AntonioGarosi/Heap/Electronic boards/core-controller/drawings/002-drills.png

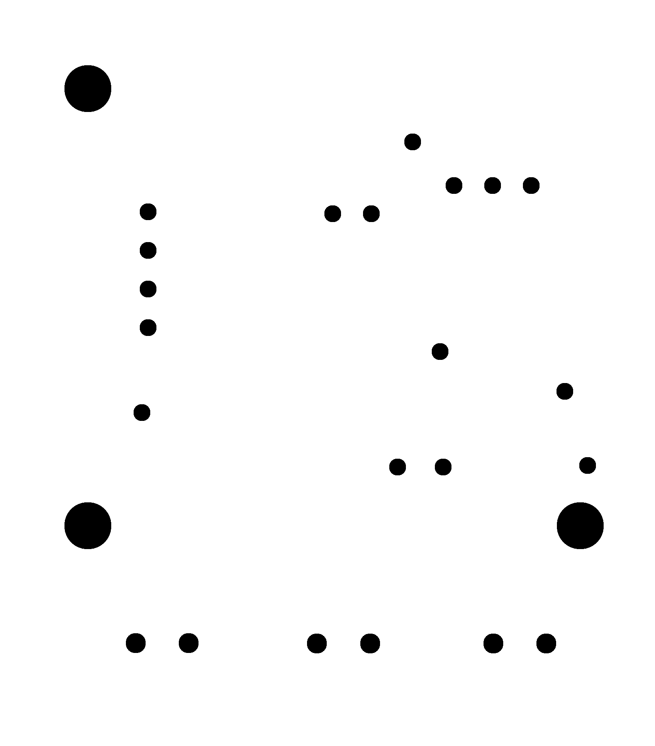
Electronic boards/core-controller/drawings/002-drills.png
