AntonioGarosi/Heap/Electronic boards/core-controller/drawings/003-outline.png

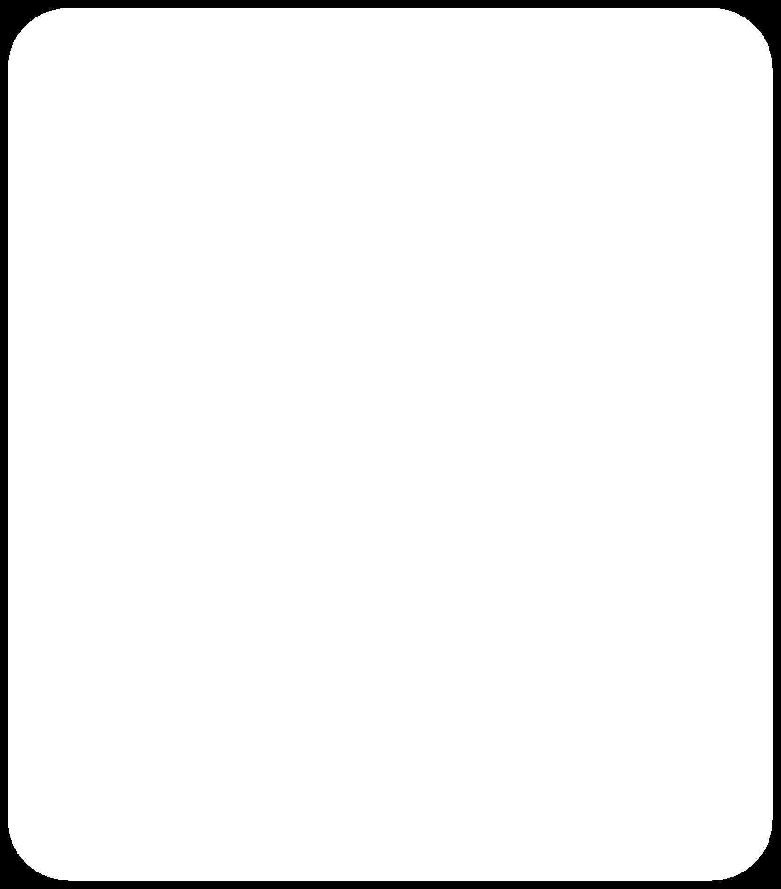
Electronic boards/core-controller/drawings/003-outline.png
