AntonioGarosi/Heap/Electronic boards/core-controller/drawings/layout.png

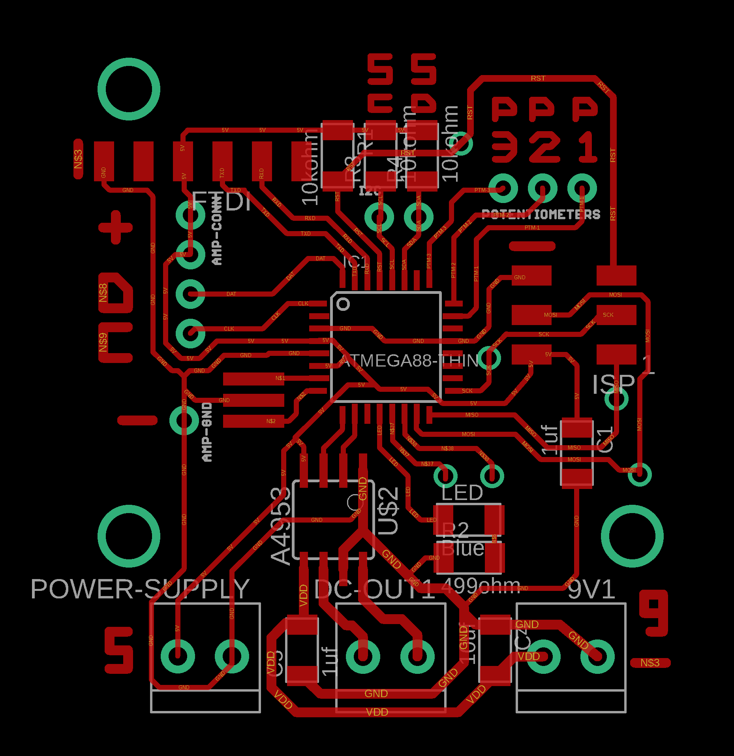
Electronic boards/core-controller/drawings/layout.png
