AntonioGarosi/Heap/Electronic boards/power-supply/drawings/001-traces.png

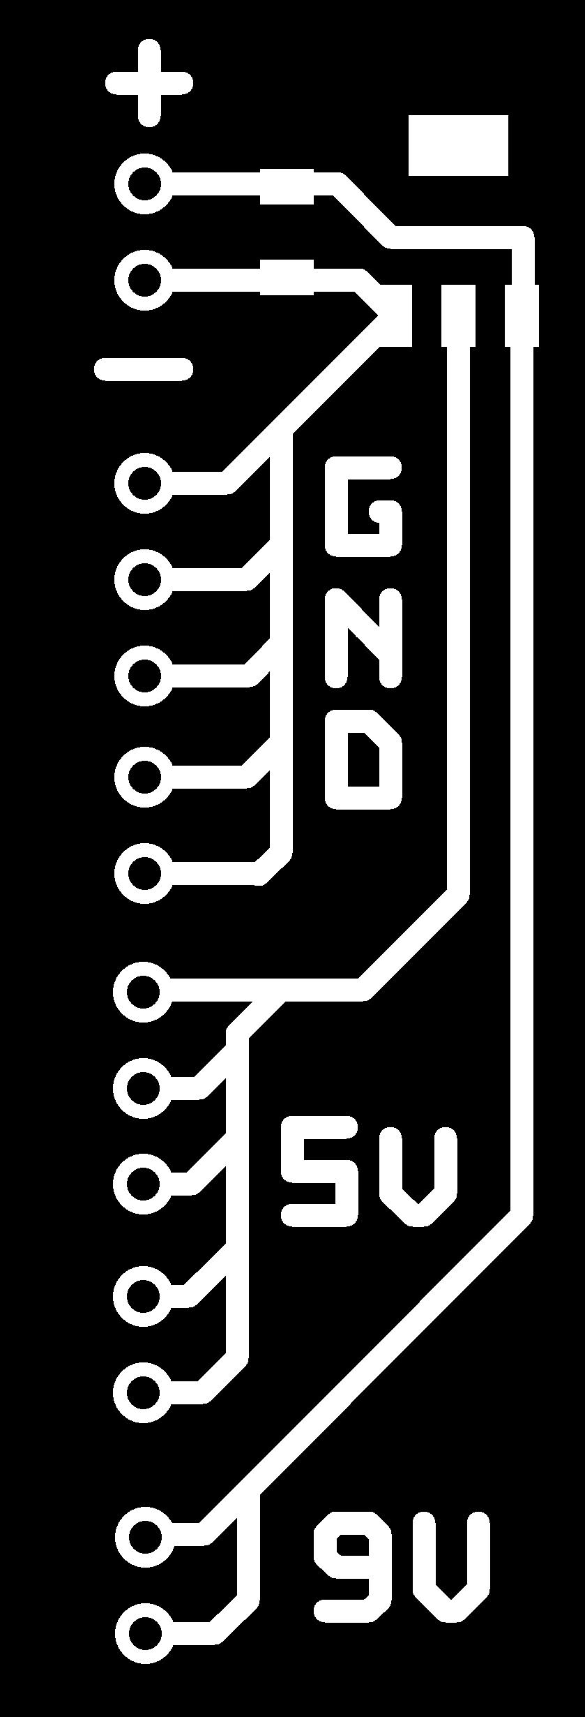
Electronic boards/power-supply/drawings/001-traces.png
