AntonioGarosi/Heap/Electronic boards/power-supply/drawings/002-drills.png

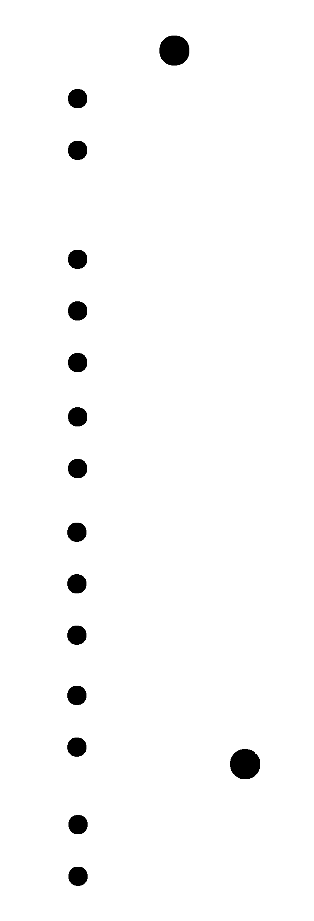
Electronic boards/power-supply/drawings/002-drills.png
