AntonioGarosi/Heap/Electronic boards/power-supply/drawings/layout.png

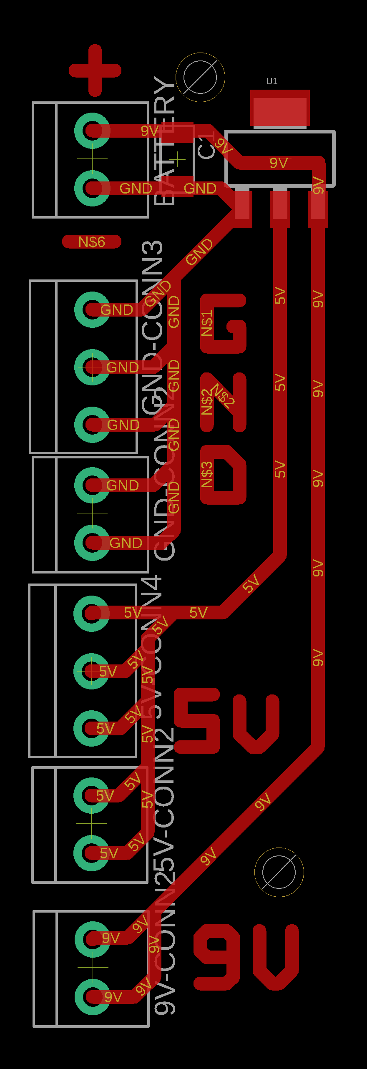
Electronic boards/power-supply/drawings/layout.png
