AntonioGarosi/Heap/Electronic boards/speaker-driver/drawings/001- traces.png

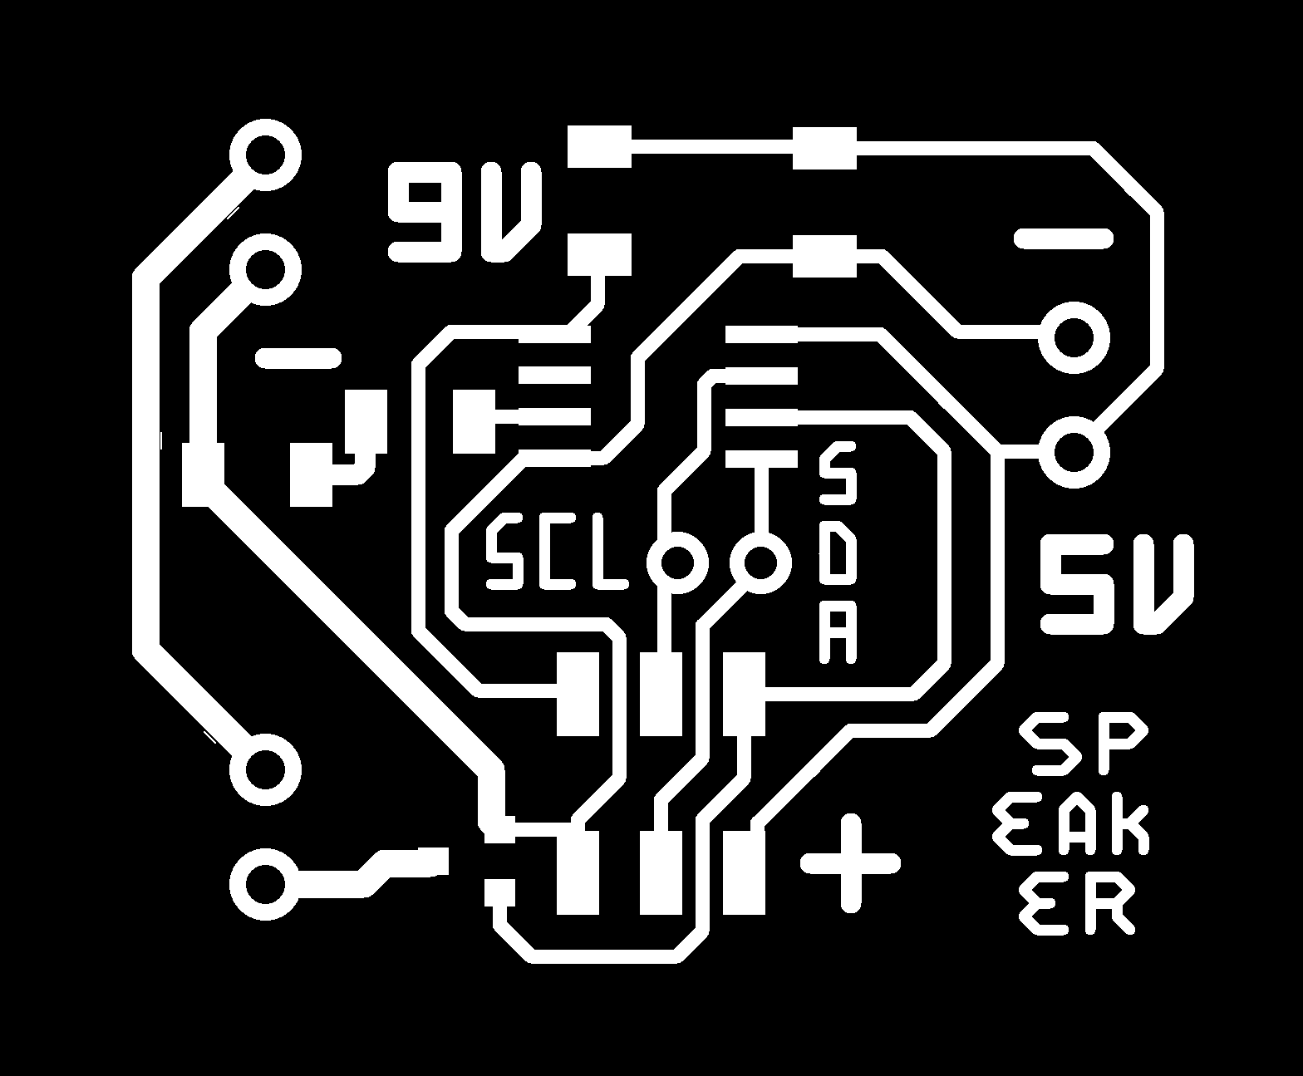
Electronic boards/speaker-driver/drawings/001- traces.png
