AntonioGarosi/Heap/Electronic boards/speaker-driver/drawings/002 - drills.png

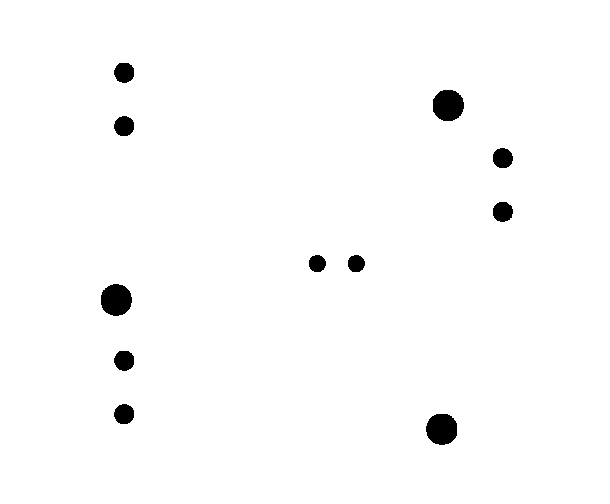
Electronic boards/speaker-driver/drawings/002 - drills.png
