AntonioGarosi/Heap/Electronic boards/speaker-driver/drawings/schematic.png

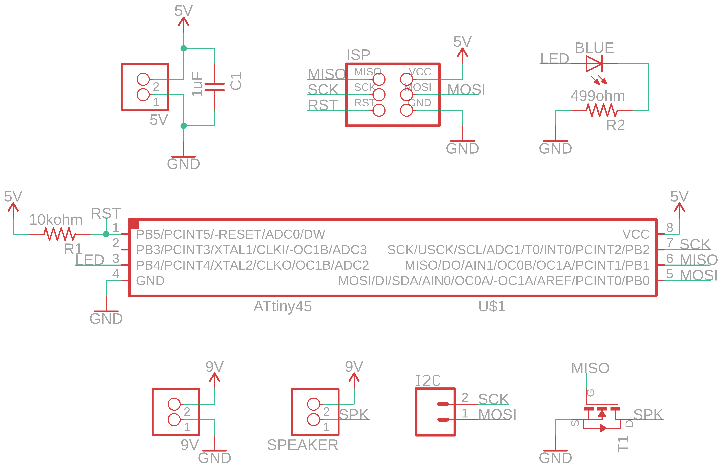
Electronic boards/speaker-driver/drawings/schematic.png
