AntonioGarosi/Heap/First prototype/Electronic boards/core-controller/drawings/001-traces.png

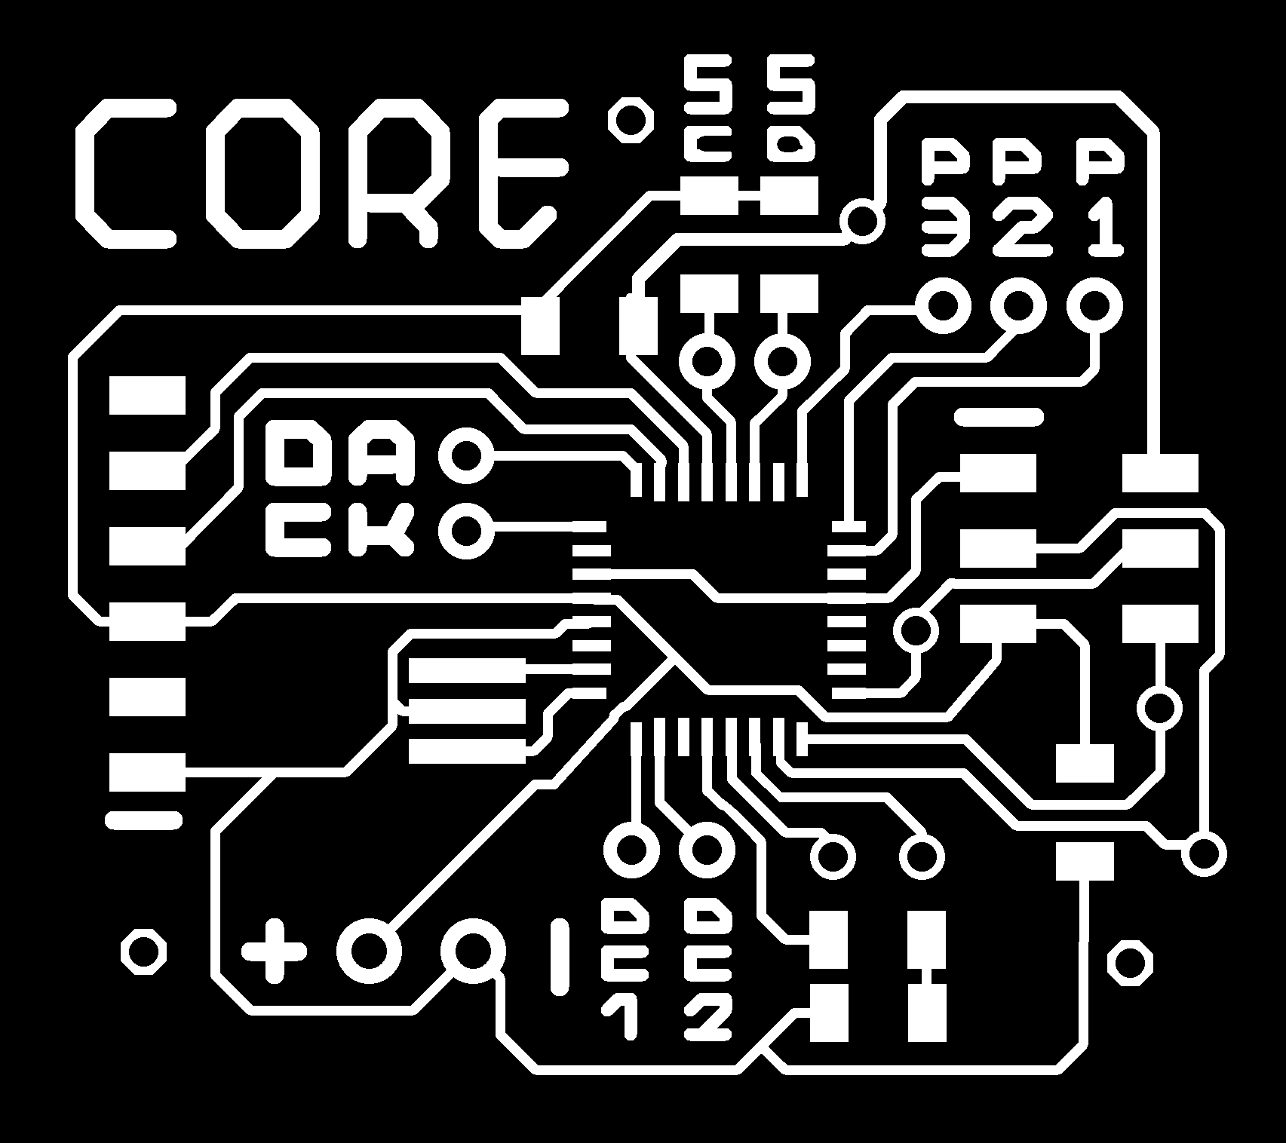
First prototype/Electronic boards/core-controller/drawings/001-traces.png
