AntonioGarosi/Heap/First prototype/Electronic boards/core-controller/drawings/002-drills.png

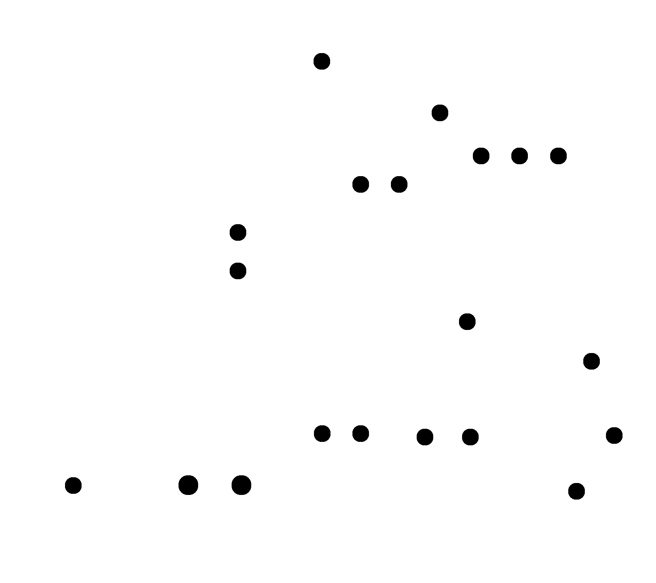
First prototype/Electronic boards/core-controller/drawings/002-drills.png
