AntonioGarosi/Heap/First prototype/Electronic boards/dc-driver/drawings/001-traces.png

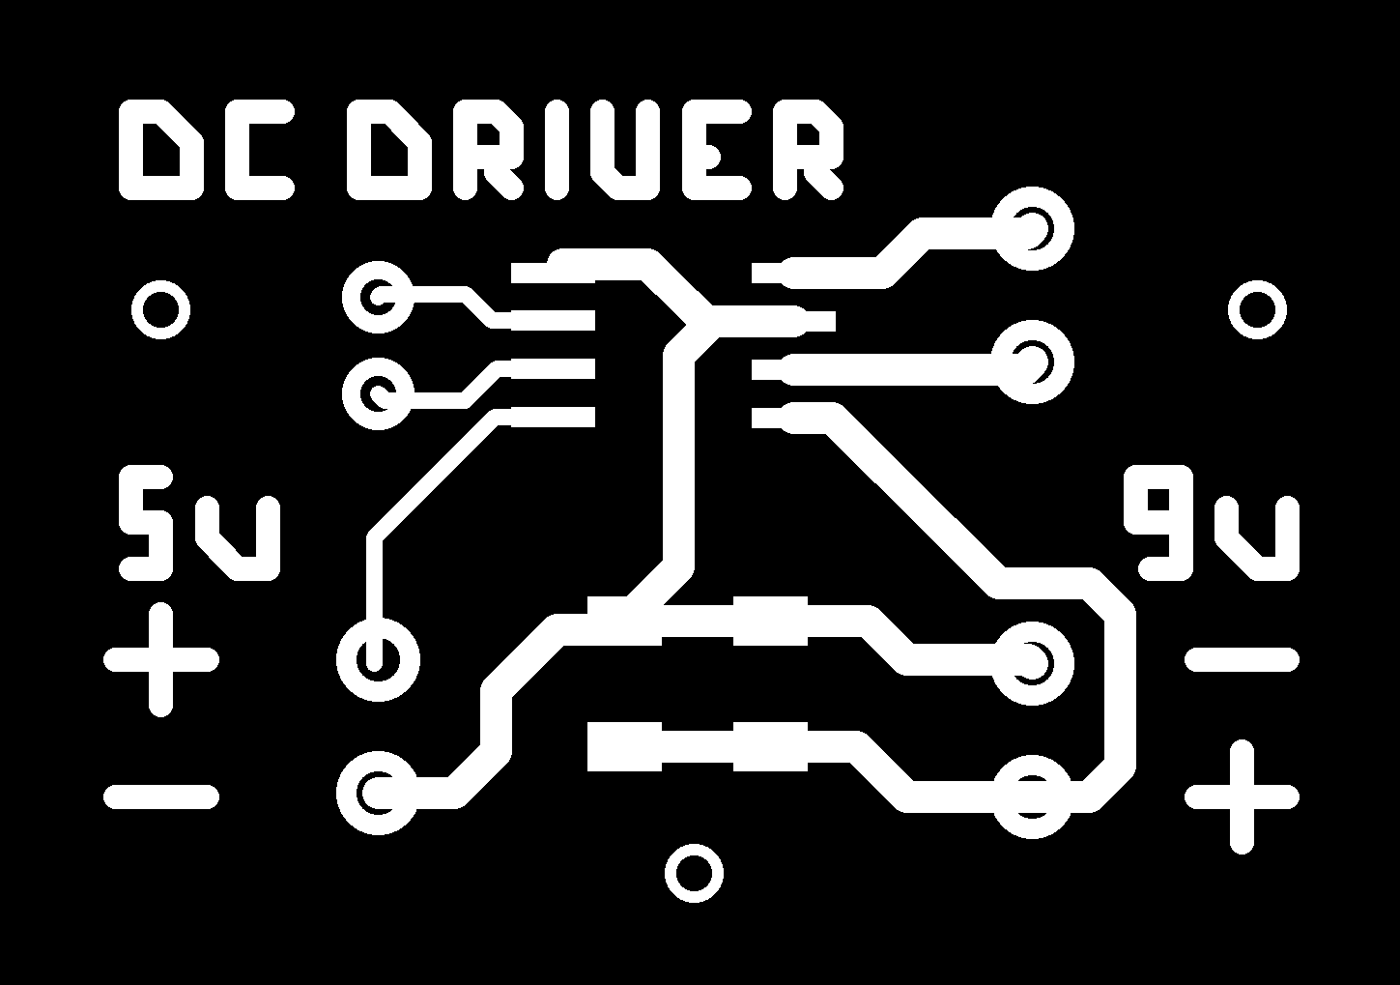
First prototype/Electronic boards/dc-driver/drawings/001-traces.png
