AntonioGarosi/Heap/First prototype/Electronic boards/dc-driver/drawings/002-drills.png

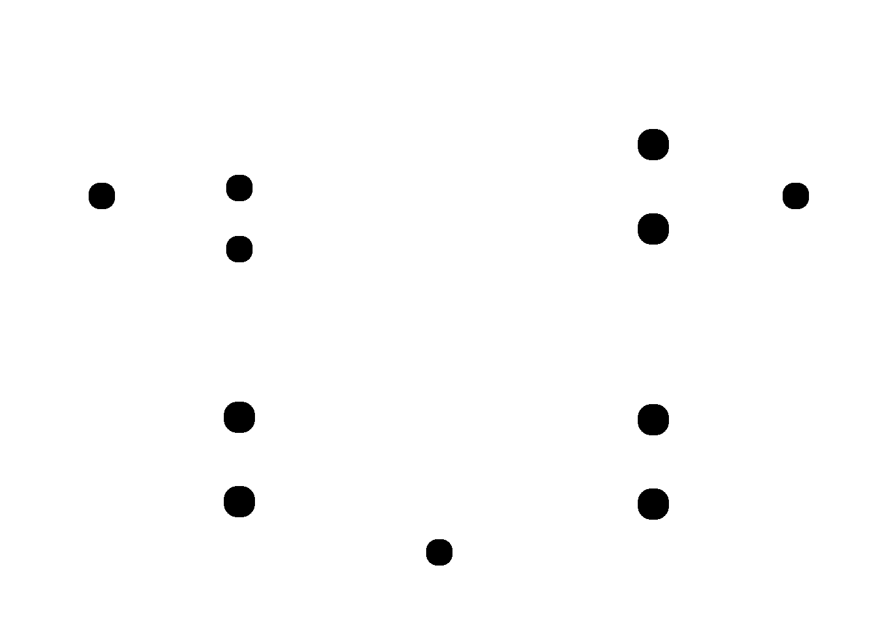
First prototype/Electronic boards/dc-driver/drawings/002-drills.png
