AntonioGarosi/Heap/First prototype/Electronic boards/power-supply/drawings/001-traces.png

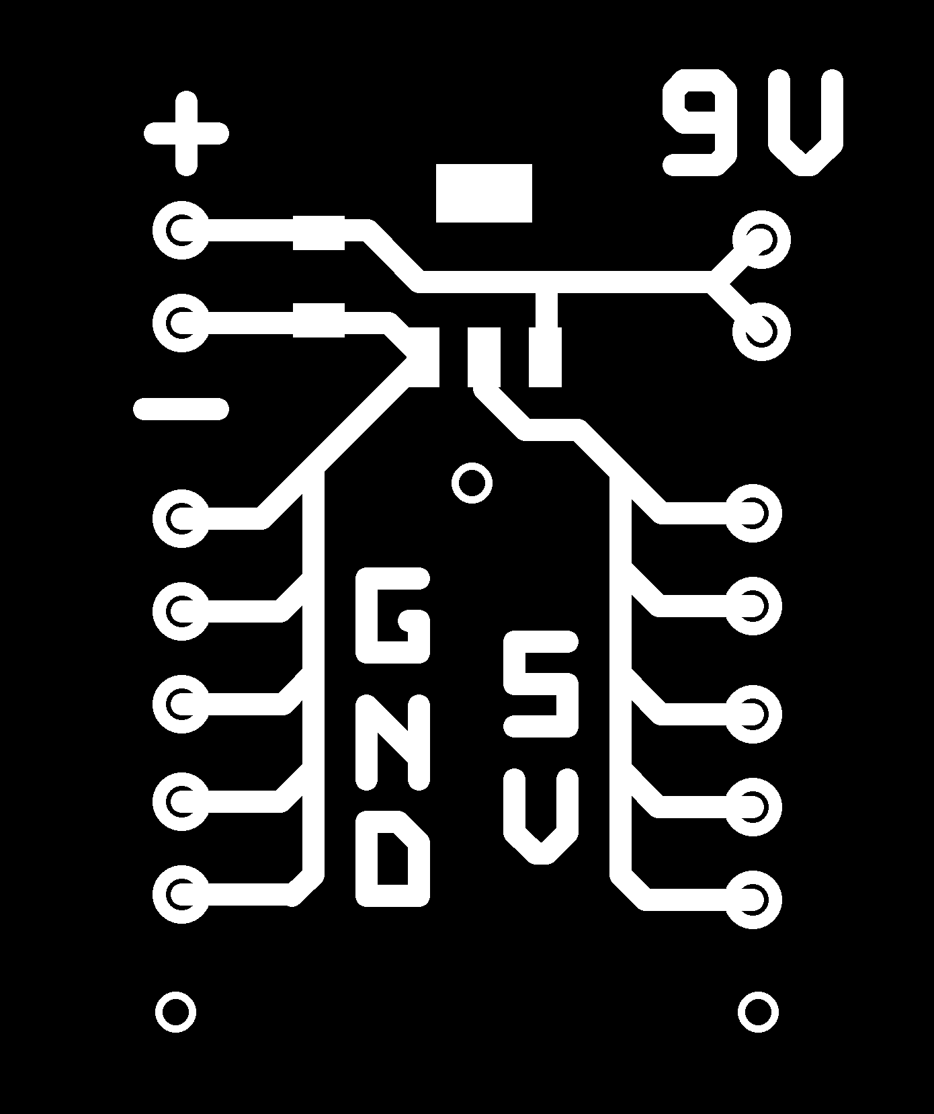
First prototype/Electronic boards/power-supply/drawings/001-traces.png
