AntonioGarosi/Heap/First prototype/Electronic boards/power-supply/drawings/002-holes.png

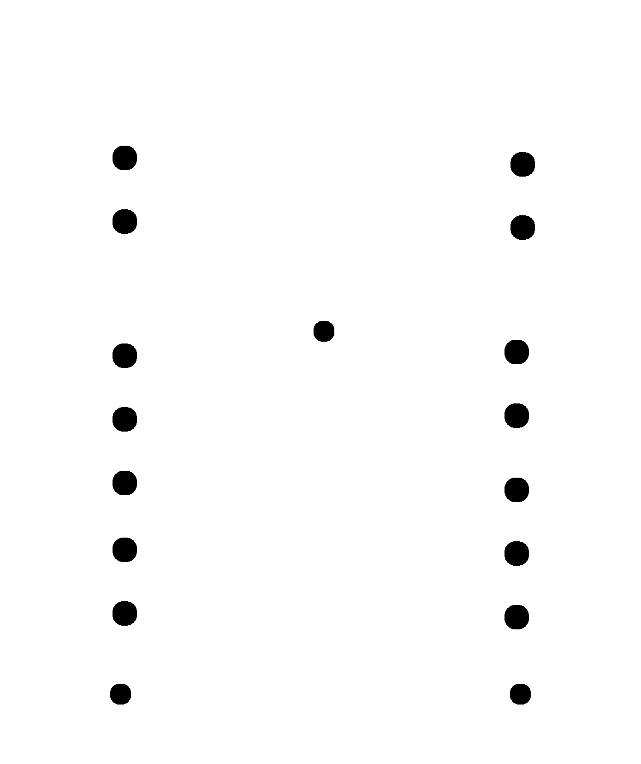
First prototype/Electronic boards/power-supply/drawings/002-holes.png
