AntonioGarosi/Heap/First prototype/Graphic designs/Cards/Drawings/card-ball.png

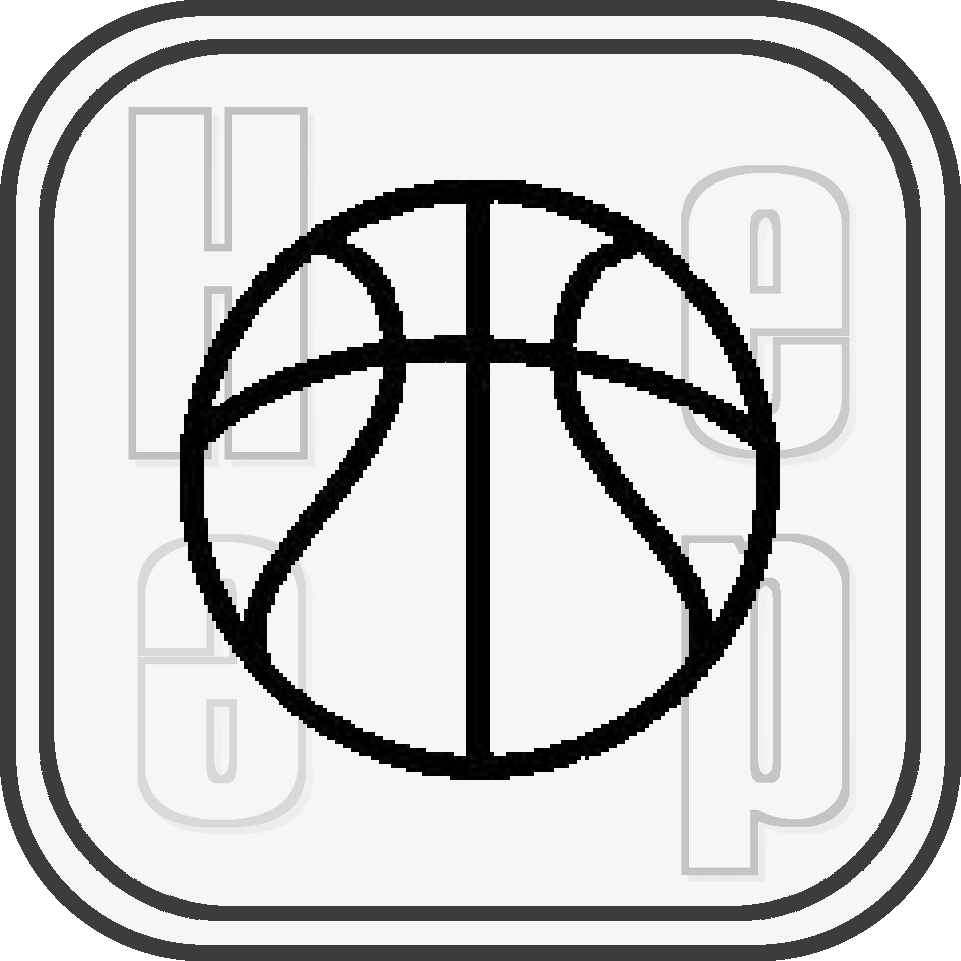
First prototype/Graphic designs/Cards/Drawings/card-ball.png
