AntonioGarosi/Heap/First prototype/Graphic designs/Cards/Drawings/card-book.png

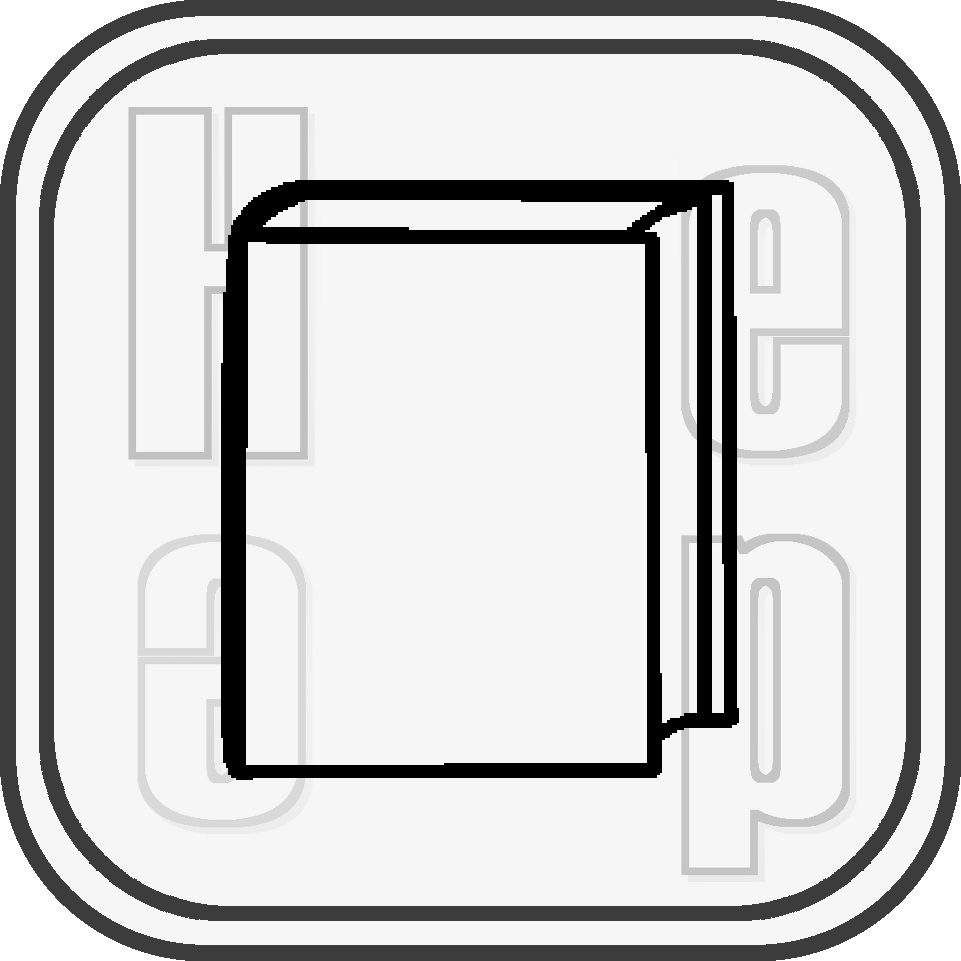
First prototype/Graphic designs/Cards/Drawings/card-book.png
