AntonioGarosi/Heap/First prototype/Graphic designs/Cards/Drawings/card-bottle.png

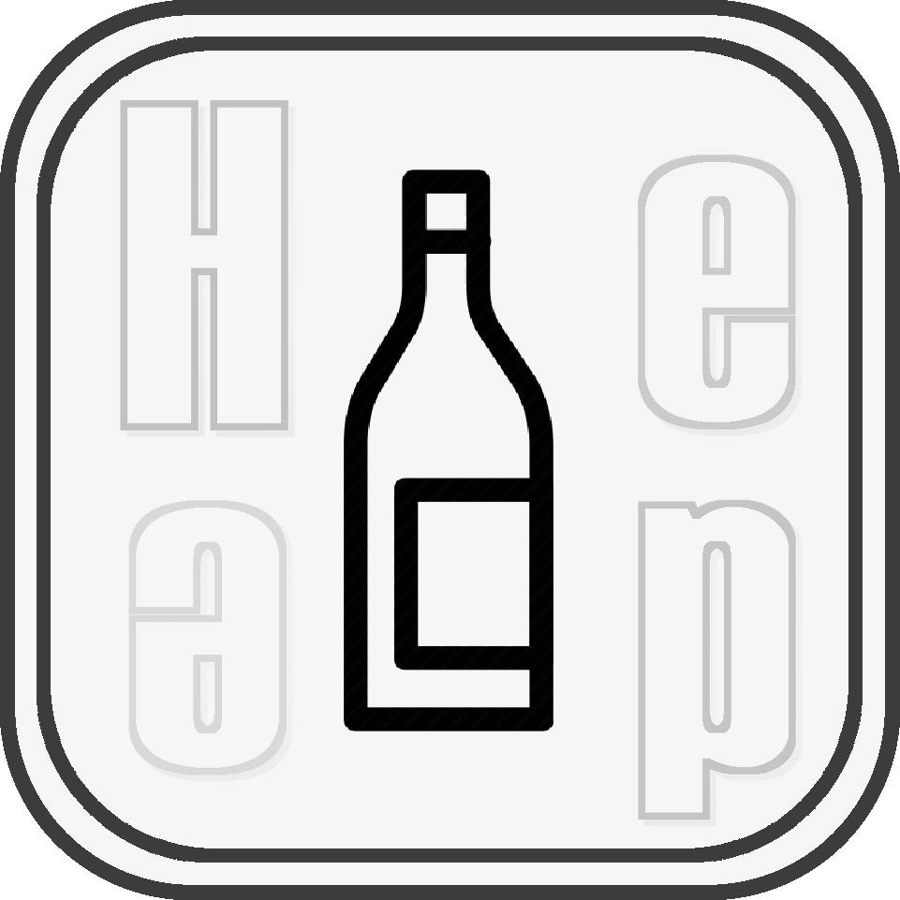
First prototype/Graphic designs/Cards/Drawings/card-bottle.png
