AntonioGarosi/Heap/First prototype/Graphic designs/Cards/Drawings/card-bottom.png

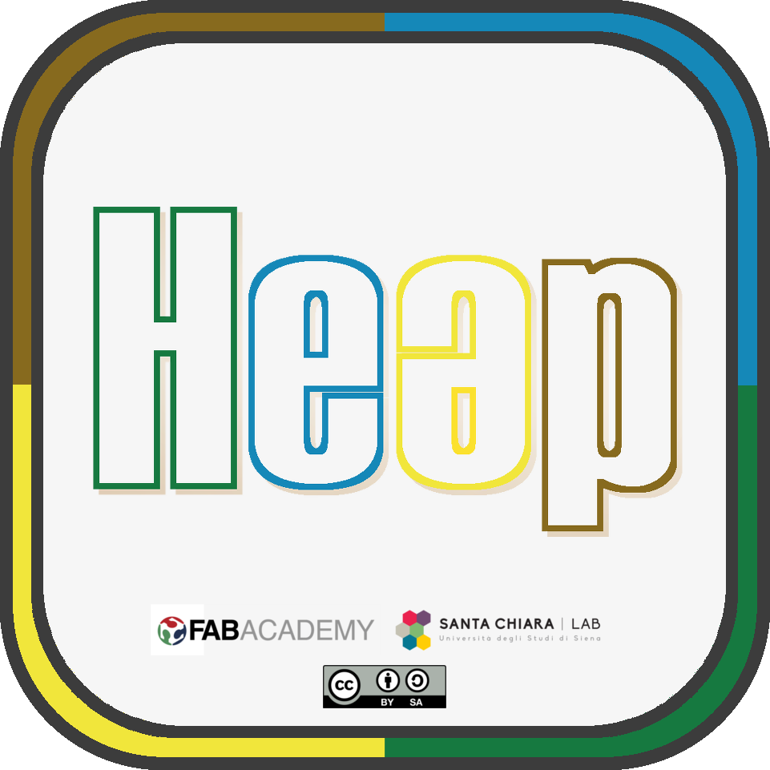
First prototype/Graphic designs/Cards/Drawings/card-bottom.png
