AntonioGarosi/Heap/First prototype/Graphic designs/Cards/Drawings/card-box.png

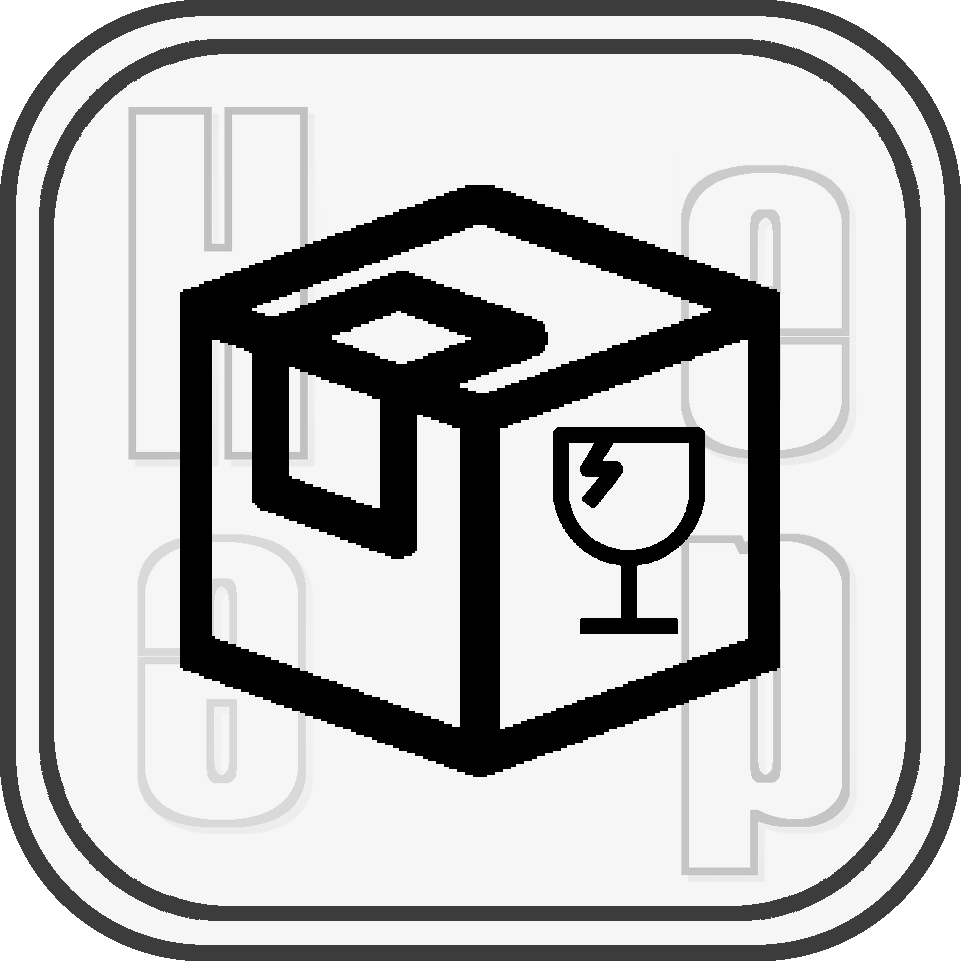
First prototype/Graphic designs/Cards/Drawings/card-box.png
