AntonioGarosi/Heap/First prototype/Graphic designs/Cards/Drawings/card-painting.png

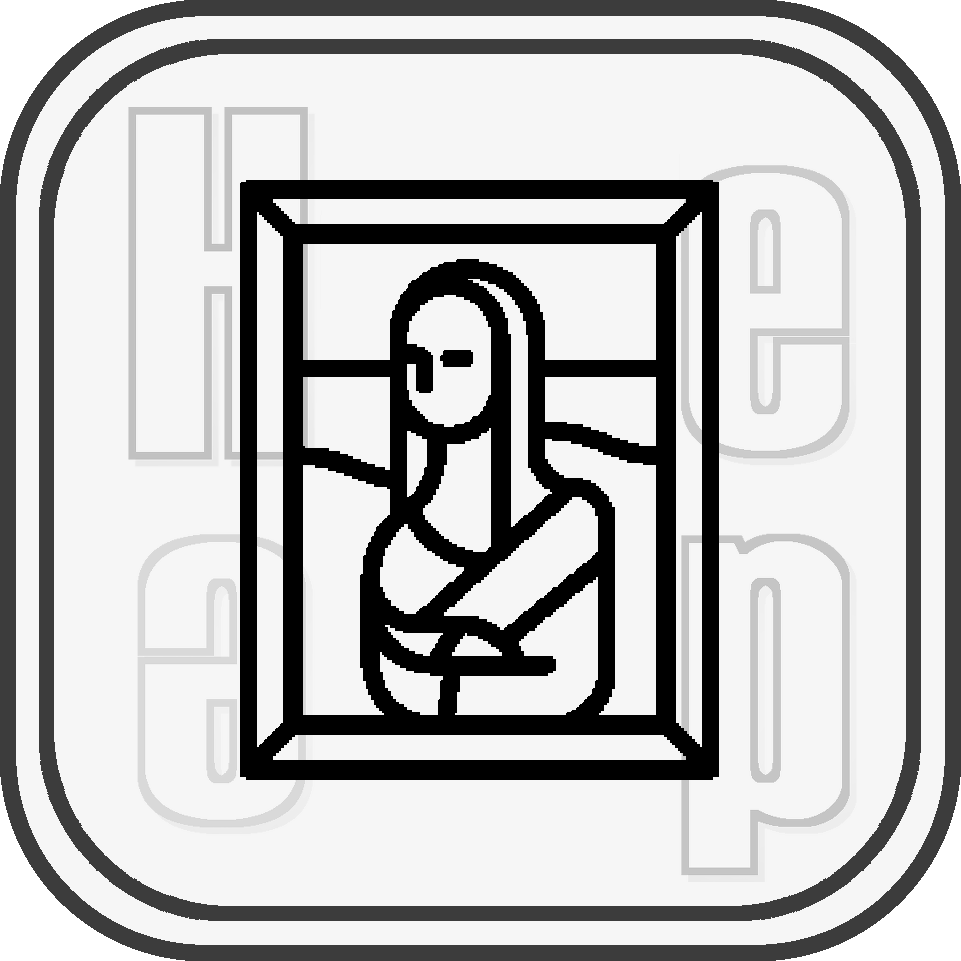
First prototype/Graphic designs/Cards/Drawings/card-painting.png
