AntonioGarosi/Heap/First prototype/Graphic designs/Cards/Drawings/card-paper-tissue.png

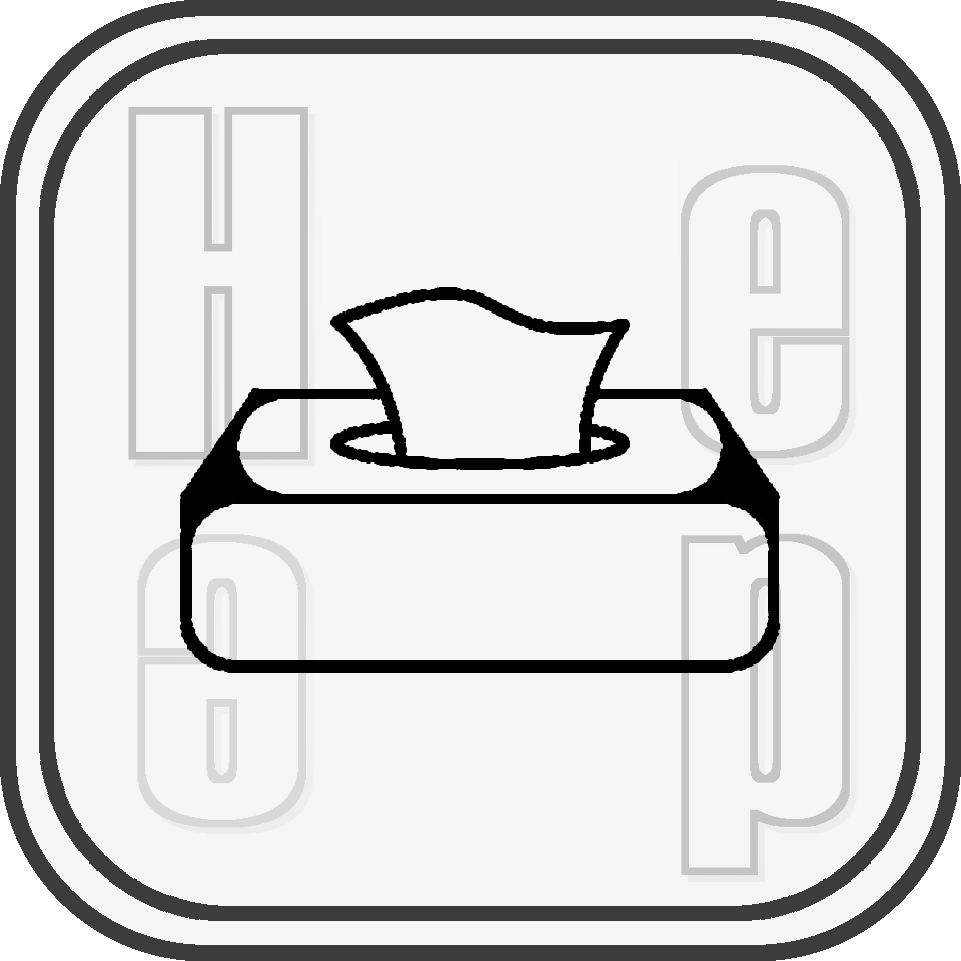
First prototype/Graphic designs/Cards/Drawings/card-paper-tissue.png
