AntonioGarosi/Heap/First prototype/Graphic designs/Cards/Drawings/card-top-template.png

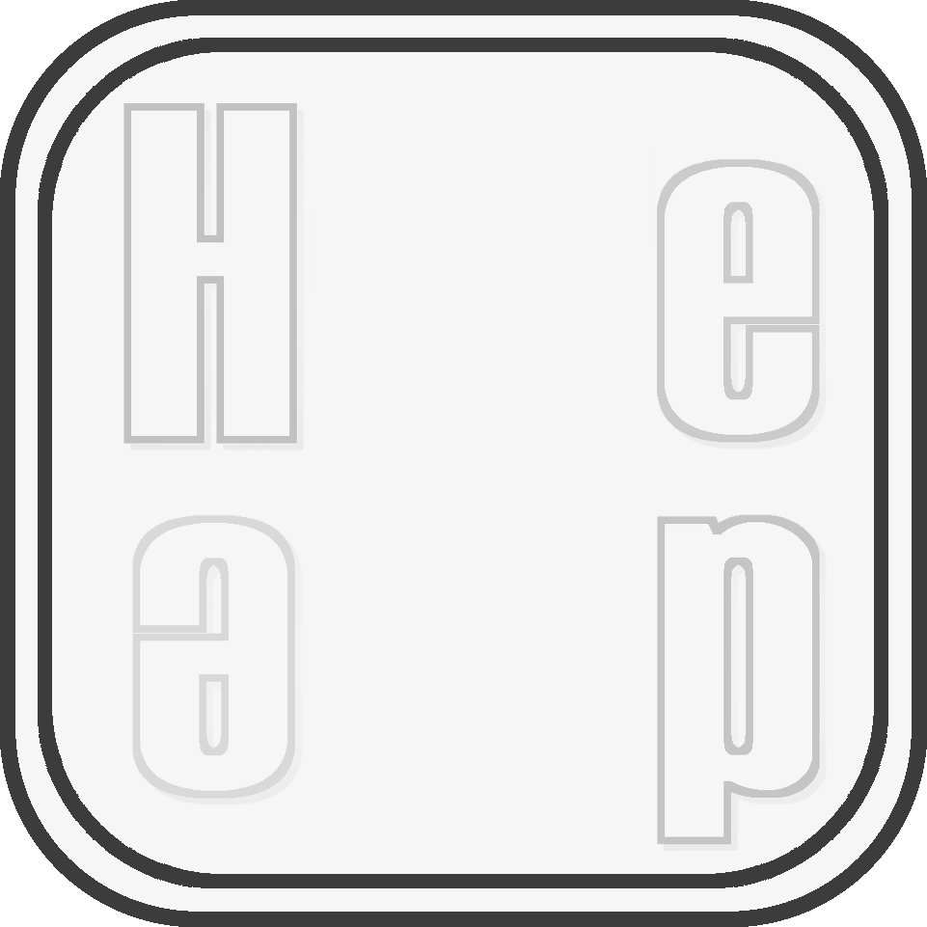
First prototype/Graphic designs/Cards/Drawings/card-top-template.png
