AntonioGarosi/Heap/First prototype/Graphic designs/Cards/Drawings/card-tv.png

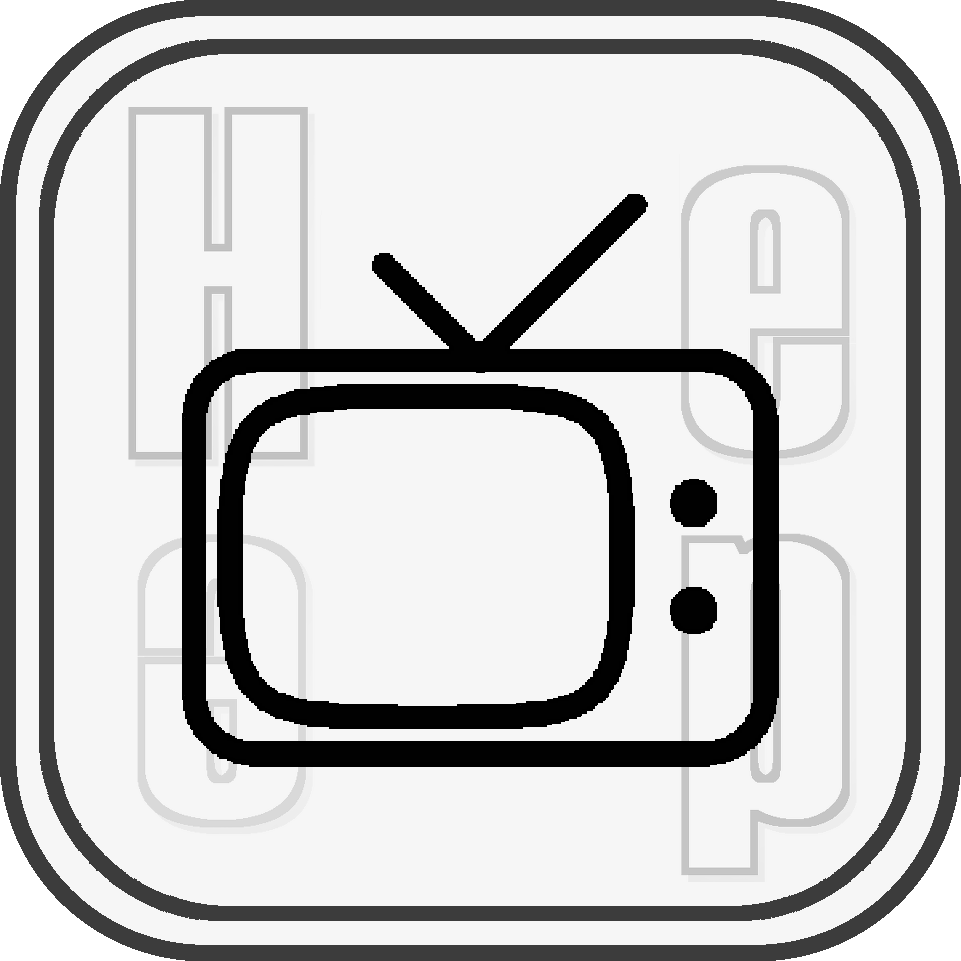
First prototype/Graphic designs/Cards/Drawings/card-tv.png
