AntonioGarosi/Heap/First prototype/Graphic designs/Cards/Drawings/card-umbrella.png

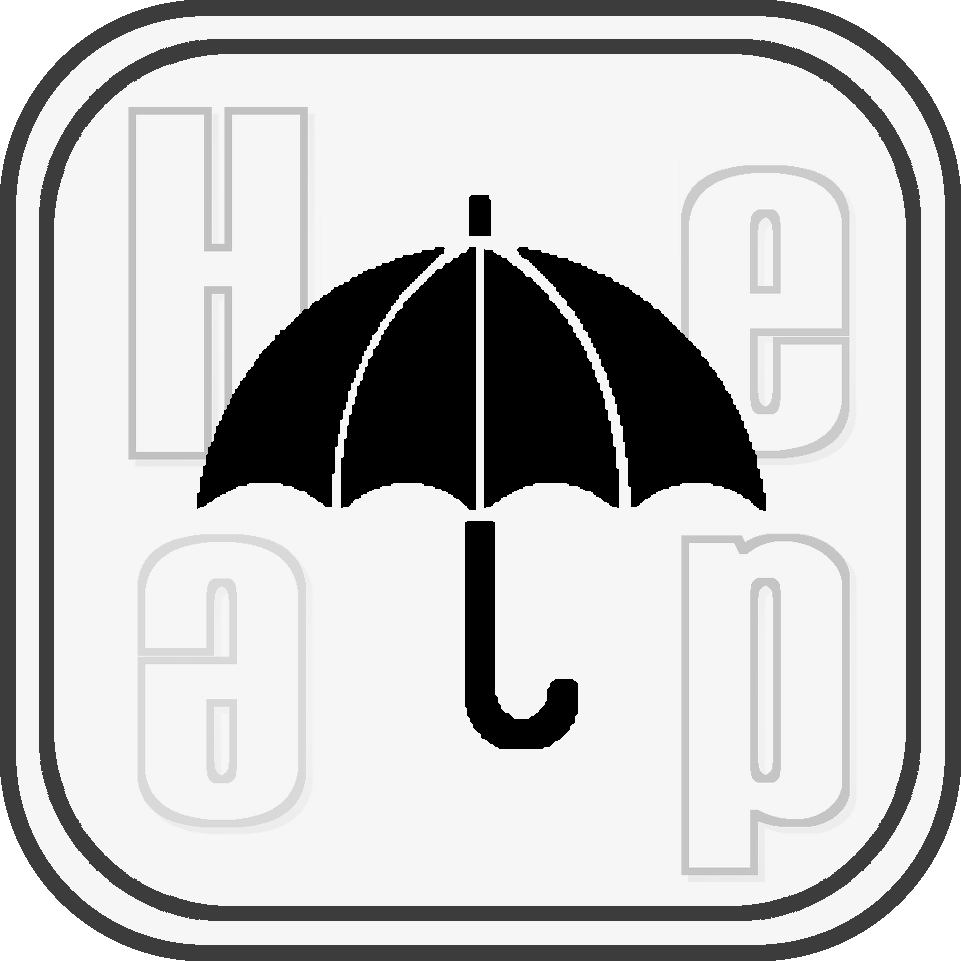
First prototype/Graphic designs/Cards/Drawings/card-umbrella.png
