AntonioGarosi/Heap/Graphic designs/Cards/Drawings/0.png

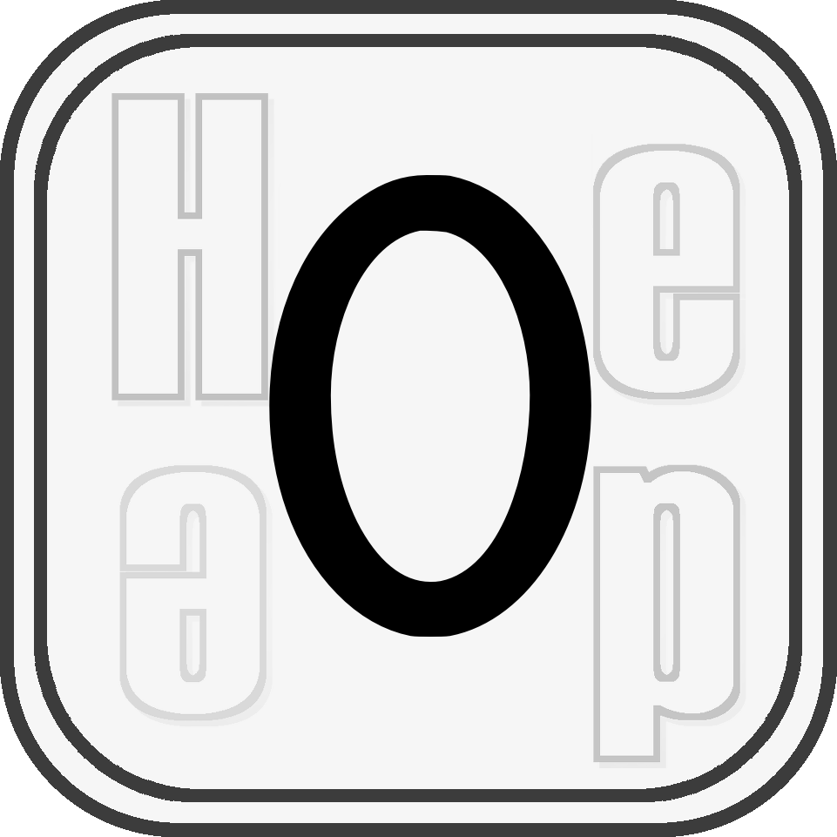
Graphic designs/Cards/Drawings/0.png
