AntonioGarosi/Heap/Graphic designs/Cards/Drawings/1.png

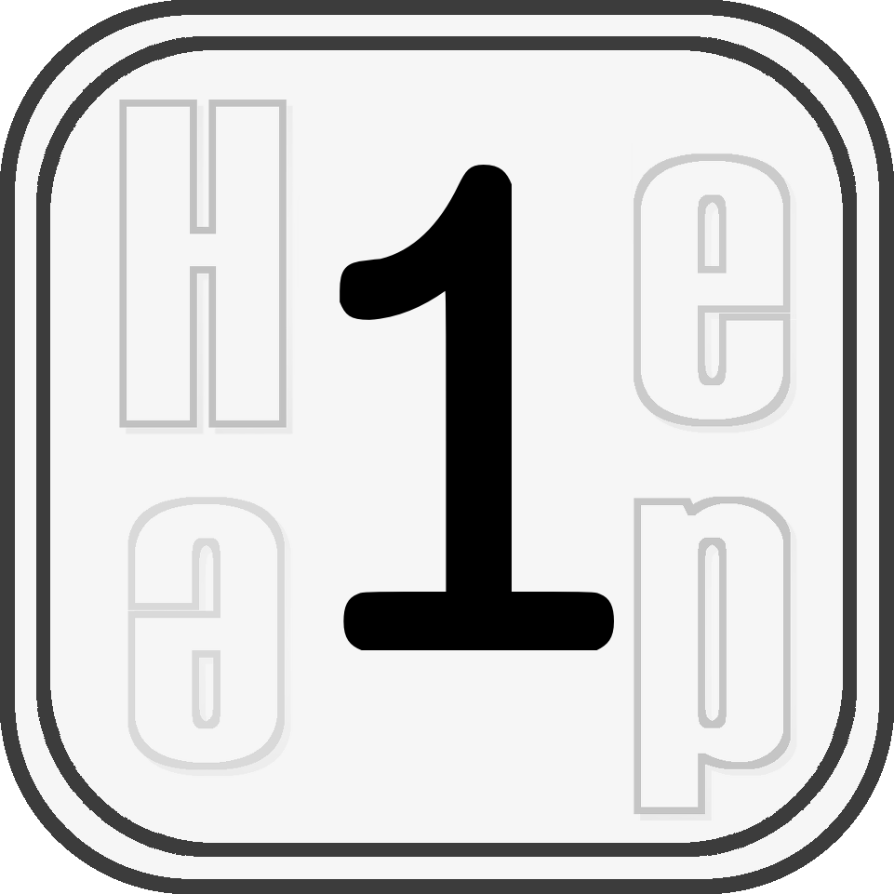
Graphic designs/Cards/Drawings/1.png
