AntonioGarosi/Heap/Graphic designs/Cards/Drawings/2.png

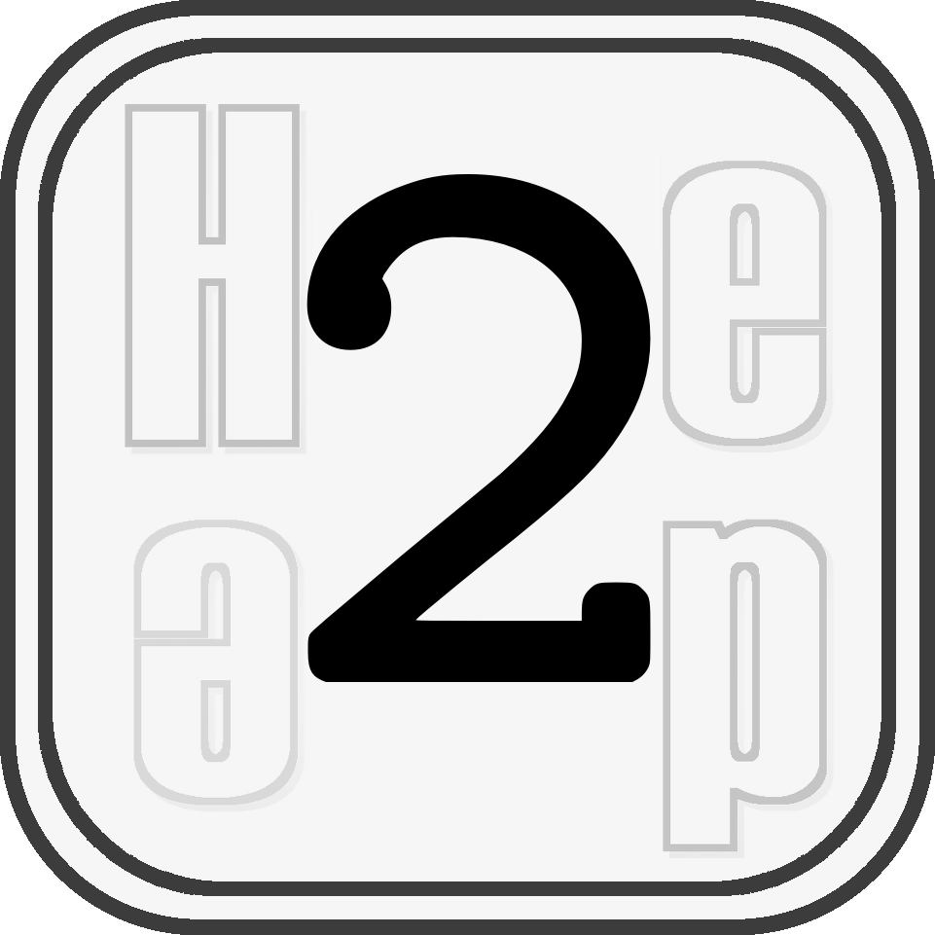
Graphic designs/Cards/Drawings/2.png
