AntonioGarosi/Heap/Graphic designs/Cards/Drawings/3.png

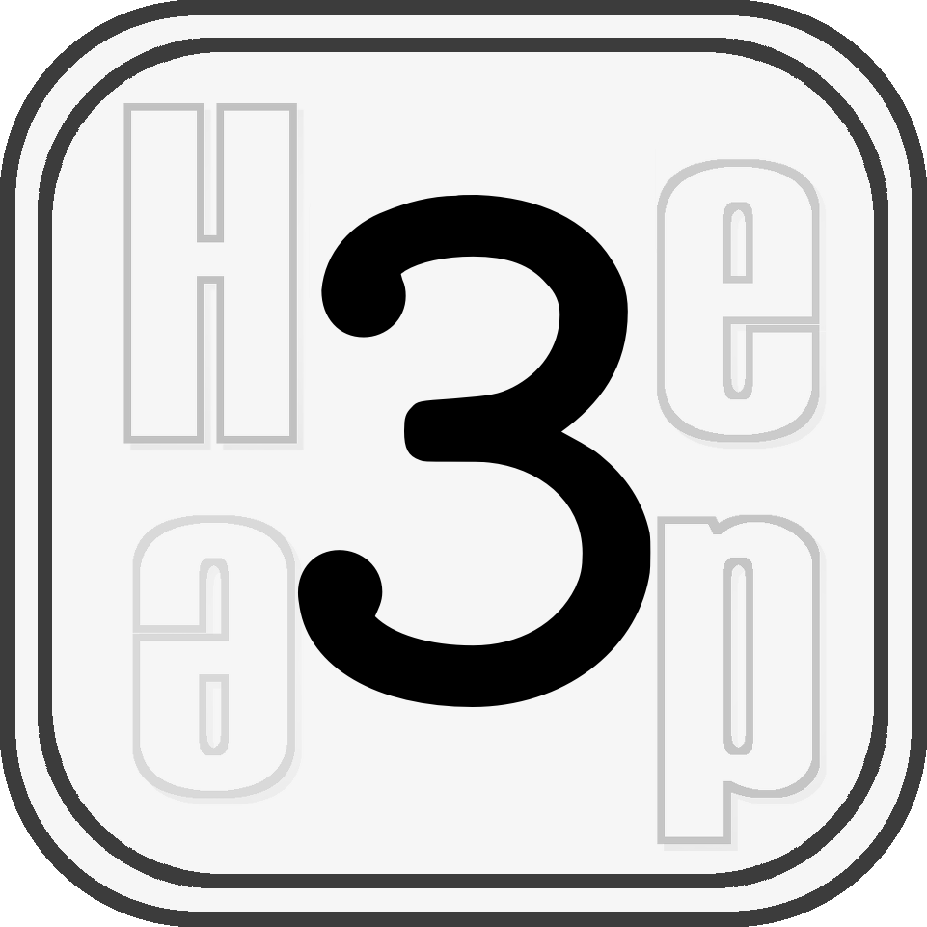
Graphic designs/Cards/Drawings/3.png
