AntonioGarosi/Heap/Graphic designs/Cards/Drawings/4.png

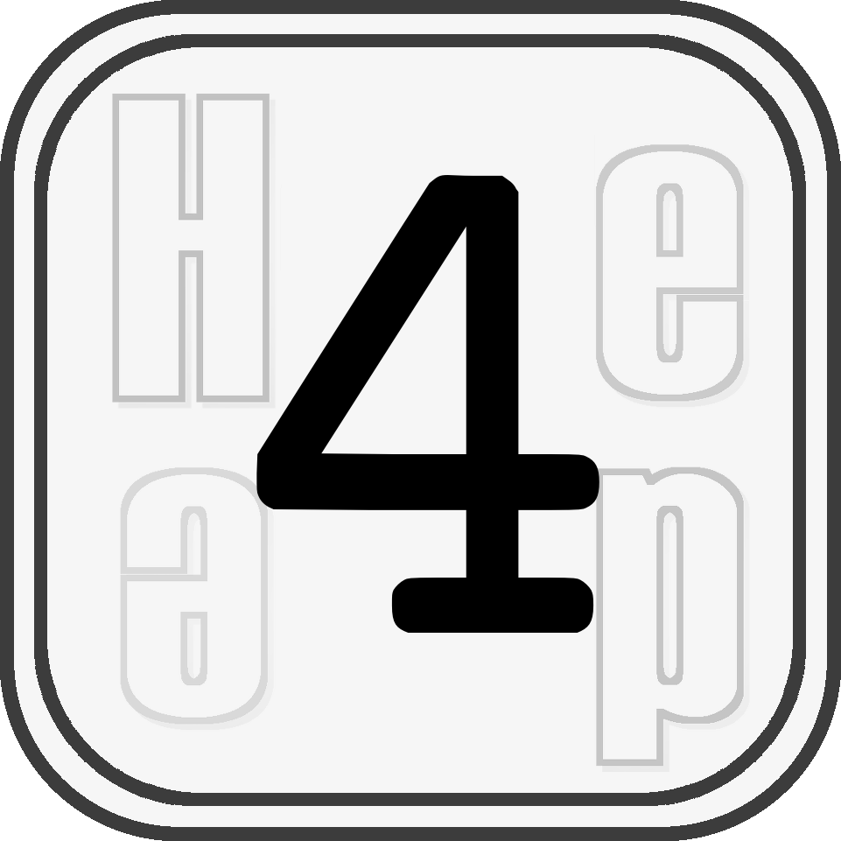
Graphic designs/Cards/Drawings/4.png
