AntonioGarosi/Heap/Graphic designs/Cards/Drawings/5.png

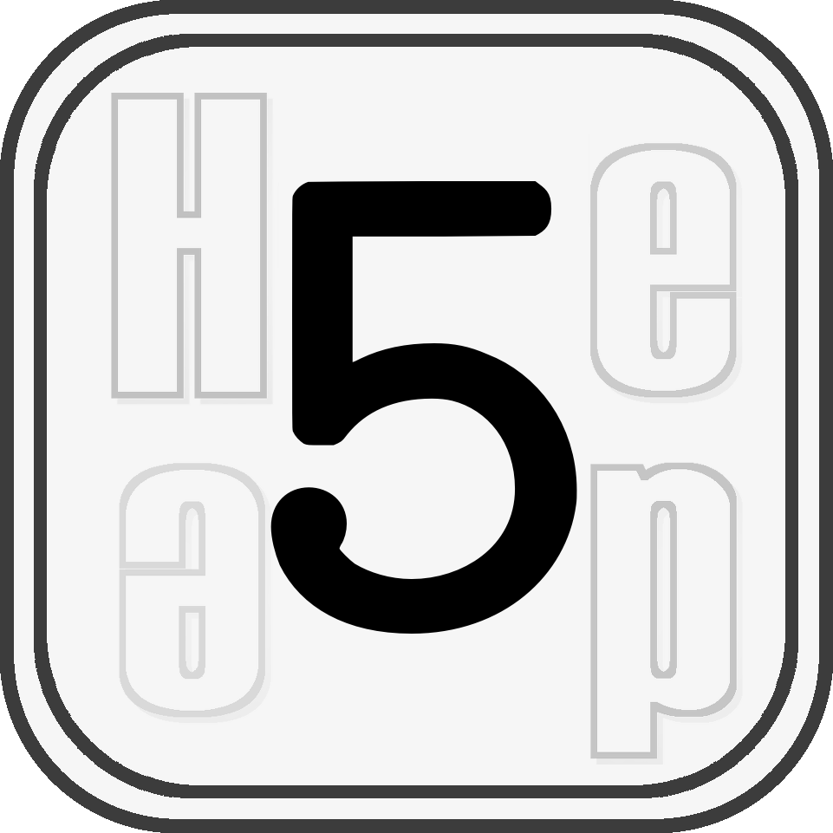
Graphic designs/Cards/Drawings/5.png
