AntonioGarosi/Heap/Graphic designs/Cards/Drawings/7.png

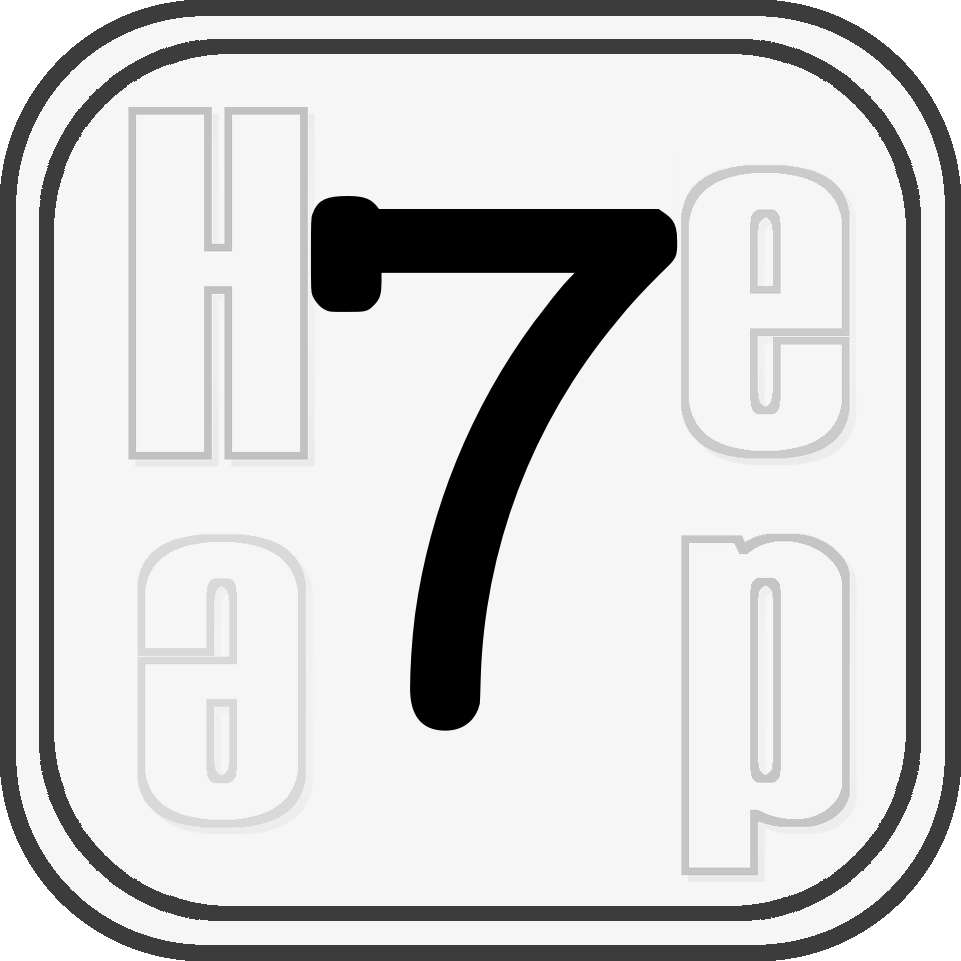
Graphic designs/Cards/Drawings/7.png
