AntonioGarosi/Heap/Presentation material/Presentation poster - ITA.png

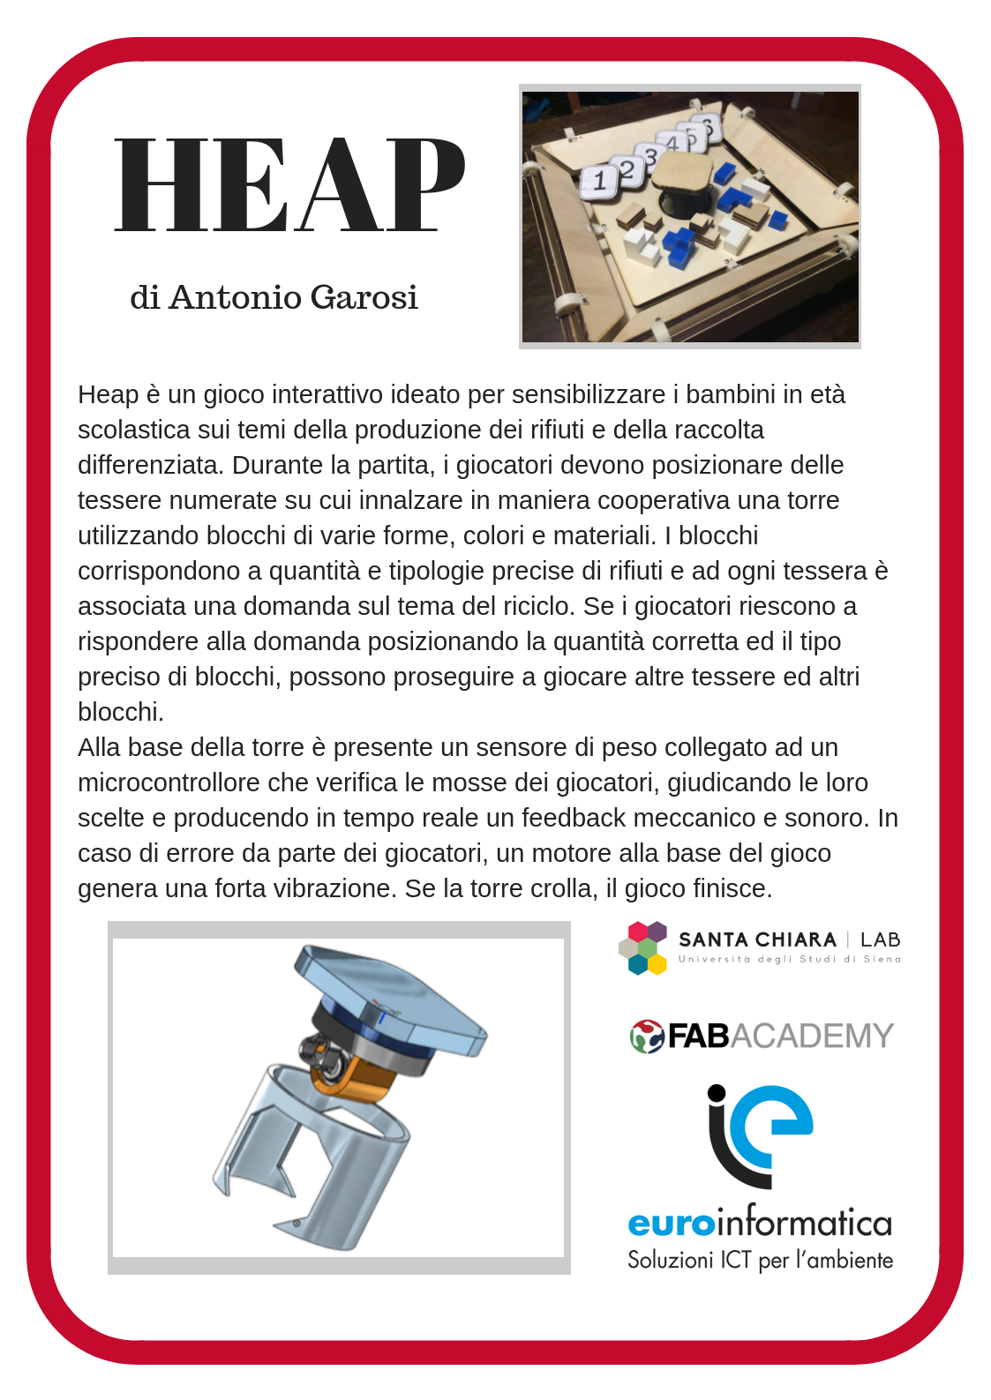
Presentation material/Presentation poster - ITA.png
