AntonioGarosi/Heap/Presentation material/Business card/front.png

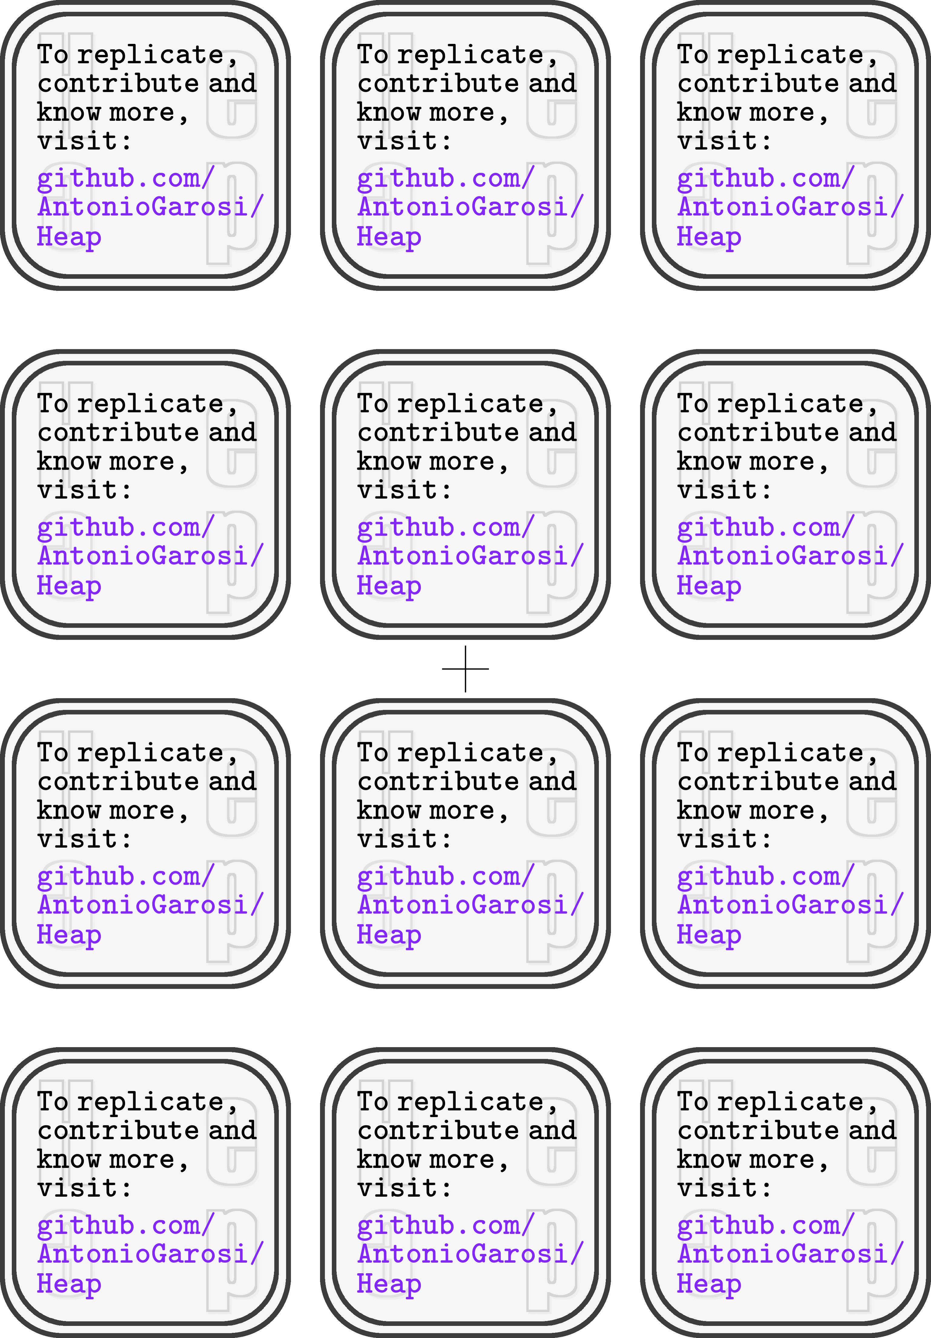
Presentation material/Business card/front.png
