AntonioGarosi/Heap/Presentation material/Business card/rear.png

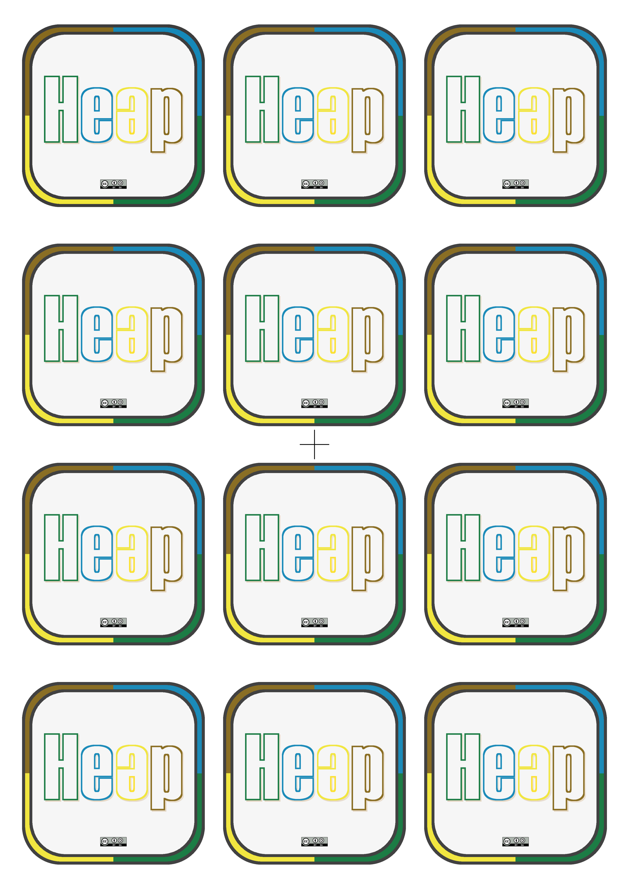
Presentation material/Business card/rear.png
